Nov4ou/ZYNQ-SoM/docs/images/schematic-pages/zynq-3.png

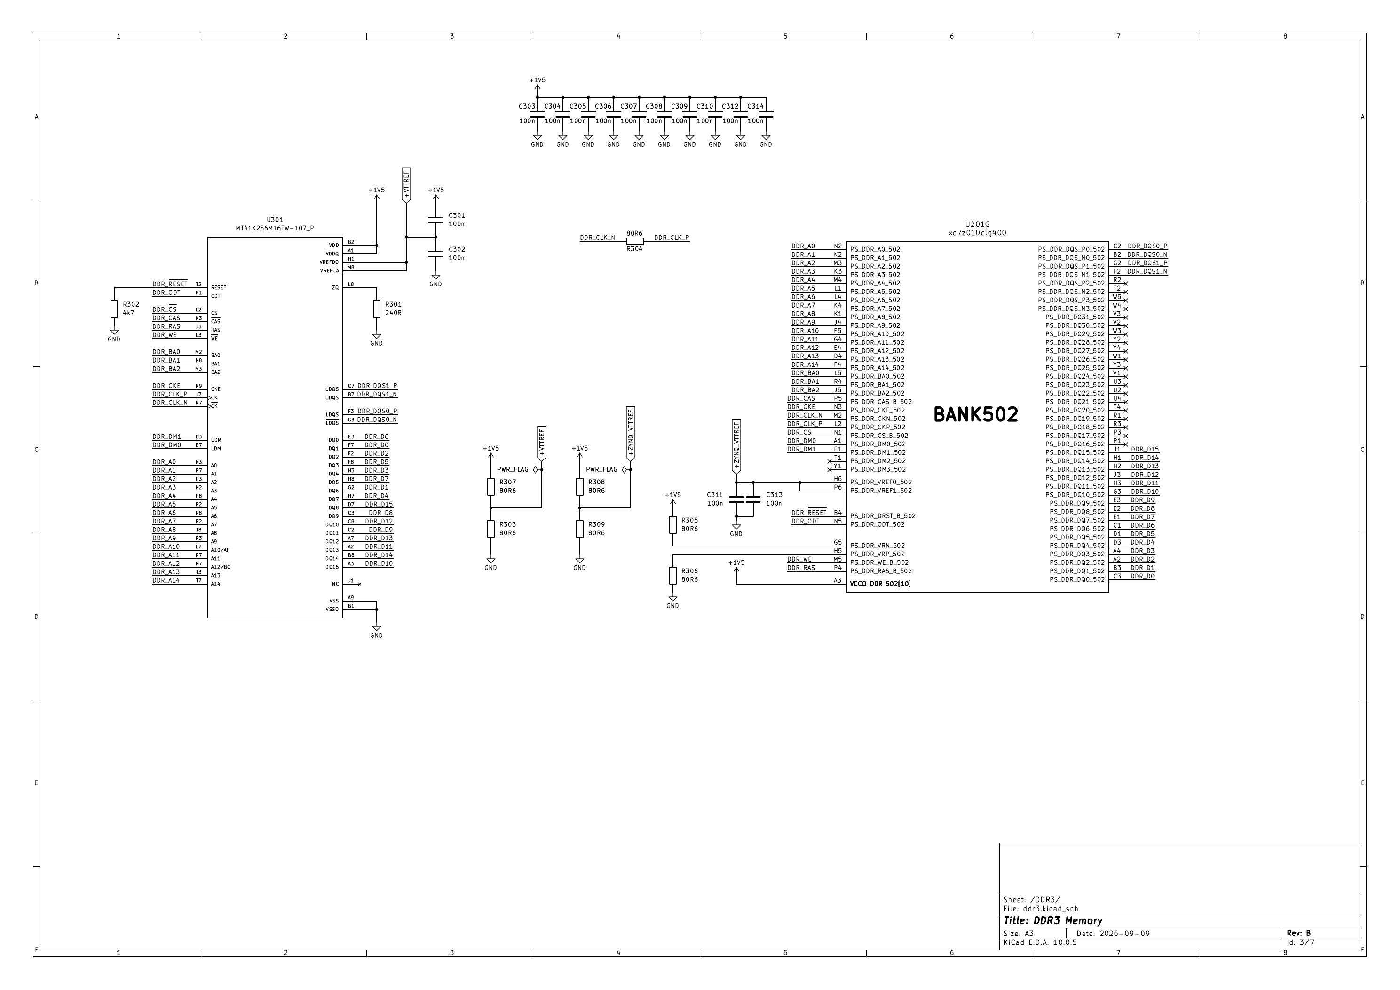
docs/images/schematic-pages/zynq-3.png
